0x46b/Polyhymnia/Code/Polyhymnia/src/Settings.cpp

#include "Settings.hpp"
#include <ArduinoJson.h>
#include <SD.h>

Settings::Settings(const char *filename) : System() {}

bool Settings::LoadSettings() {
  if (!SD.begin(BUILTIN_SDCARD)) {
    Serial.println("initialization failed!");
    _loadedSuccessfully = false;
    return false;
  }

  File input = SD.open(_filename, FILE_READ);
  JsonDocument doc;

  DeserializationError error = deserializeJson(doc, input);
  input.close();

  if (error) {
    Serial.print("deserializeJson() failed: ");
    Serial.println(error.c_str());
    return false;
  }

  JsonObject settings = doc["settings"];
  System.ShowBootscreen = settings["ShowBootscreen"];         // "true"
  System.BootscreenFilepath = settings["BootscreenFilepath"]; // nullptr
  System.MidiChannel = settings["MidiChannel"];               // 1

  int patchCounter = 0;
  for (JsonObject patche : doc["patches"].as<JsonArray>()) {
    PatchSetting *currentPatch = &Patches[patchCounter];
    currentPatch->Name = patche["Name"]; // "Patch 1", "Patch 2"

    currentPatch->DCO1.Waveform = patche["VCO1"]["Type"]; // 1, 1
    currentPatch->DCO1.Detune = patche["VCO1"]["Detune"]; // 0, 0

    currentPatch->DCO2.Waveform = patche["VCO2"]["Type"]; // 1, 1
    currentPatch->DCO2.Detune = patche["VCO2"]["Detune"]; // 0, 0

    currentPatch->DCO3.Waveform = patche["VCO3"]["Type"]; // 1, 1
    currentPatch->DCO3.Detune = patche["VCO3"]["Detune"]; // 0, 0

    currentPatch->Noise.Gain = patche["Noise"]["Gain"]; // 0, 0

    JsonObject patche_Envelope = patche["Envelope"];
    currentPatch->Envelope.Attack = patche_Envelope["Attack"];   // 0, 0
    currentPatch->Envelope.Decay = patche_Envelope["Decay"];     // 35, 35
    currentPatch->Envelope.Sustain = patche_Envelope["Sustain"]; // 1, 1
    currentPatch->Envelope.Release = patche_Envelope["Release"]; // 300, 300

    JsonObject patche_Filter = patche["Filter"];
    currentPatch->Filter.Type = patche_Filter["FilterType"];     // 0, 0
    currentPatch->Filter.Cutoff = patche_Filter["Cutoff"];       // 1, 1
    currentPatch->Filter.Resonance = patche_Filter["Resonance"]; // 0, 0

    currentPatch->LFO.Rate = patche["LFO"]["Rate"];     // 10, 10
    currentPatch->LFO.Amount = patche["LFO"]["Amount"]; // 50, 50

    JsonObject patche_Mixer = patche["Mixer"];
    currentPatch->Mixer.DCO1Gain = patche_Mixer["VCO1Gain"];   // 0.3, 0.3
    currentPatch->Mixer.DCO2Gain = patche_Mixer["VCO2Gain"];   // 0.3, 0.3
    currentPatch->Mixer.DCO3Gain = patche_Mixer["VCO3Gain"];   // 0.3, 0.3
    currentPatch->Mixer.NoiseGain = patche_Mixer["NoiseGain"]; // 0, 0

    patchCounter++;
  }

  _loadedSuccessfully = true;
  return true;
}

bool Settings::Save() {
  JsonDocument doc;

  JsonObject settings = doc["settings"].to<JsonObject>();
  settings["ShowBootscreen"] = System.ShowBootscreen;
  settings["BootscreenFilepath"] = System.BootscreenFilepath;
  settings["MidiChannel"] = System.MidiChannel;

  JsonArray patches = doc["patches"].to<JsonArray>();

  for (int i = 0; i <= NUMBER_OF_PATCHES; i++) {
    JsonObject patches_0 = patches.add<JsonObject>();
    patches_0["Name"] = Patches[i].Name;

    JsonObject patches_0_VCO1 = patches_0["DCO1"].to<JsonObject>();
    patches_0_VCO1["Type"] = Patches[i].DCO1.Waveform;
    patches_0_VCO1["Detune"] = Patches[i].DCO1.Detune;

    JsonObject patches_0_VCO2 = patches_0["DCO2"].to<JsonObject>();
    patches_0_VCO2["Type"] = Patches[i].DCO2.Waveform;
    patches_0_VCO2["Detune"] = Patches[i].DCO2.Detune;

    JsonObject patches_0_VCO3 = patches_0["DCO3"].to<JsonObject>();
    patches_0_VCO3["Type"] = Patches[i].DCO3.Waveform;
    patches_0_VCO3["Detune"] = Patches[i].DCO3.Detune;
    patches_0["Noise"]["Gain"] = Patches[i].Noise.Gain;

    JsonObject patches_0_Envelope = patches_0["Envelope"].to<JsonObject>();
    patches_0_Envelope["Attack"] = Patches[i].Envelope.Attack;
    patches_0_Envelope["Decay"] = Patches[i].Envelope.Decay;
    patches_0_Envelope["Sustain"] = Patches[i].Envelope.Sustain;
    patches_0_Envelope["Release"] = Patches[i].Envelope.Release;

    JsonObject patches_0_Filter = patches_0["Filter"].to<JsonObject>();
    patches_0_Filter["FilterType"] = Patches[i].Filter.Type;
    patches_0_Filter["Cutoff"] = Patches[i].Filter.Cutoff;
    patches_0_Filter["Resonance"] = Patches[i].Filter.Resonance;

    JsonObject patches_0_LFO = patches_0["LFO"].to<JsonObject>();
    patches_0_LFO["Rate"] = Patches[i].LFO.Rate;
    patches_0_LFO["Amount"] = Patches[i].LFO.Amount;

    JsonObject patches_0_Mixer = patches_0["Mixer"].to<JsonObject>();
    patches_0_Mixer["DCO1Gain"] = Patches[i].Mixer.DCO1Gain;
    patches_0_Mixer["DCO2Gain"] = Patches[i].Mixer.DCO2Gain;
    patches_0_Mixer["DCO3Gain"] = Patches[i].Mixer.DCO3Gain;
    patches_0_Mixer["NoiseGain"] = Patches[i].Mixer.NoiseGain;
  }

  String output;

  doc.shrinkToFit(); // optional

  serializeJson(doc, output);
  File outputFile = SD.open(_filename, FILE_WRITE);
  if (outputFile) {
    outputFile.print(output.c_str());

    outputFile.close();
    return true;
  }
  return false;
}

bool Settings::is_loaded() { return _loadedSuccessfully; }
