0x46b/Polyhymnia/Code/Polyhymnia/include/MIDI.hpp

#ifndef MIDI_HPP
#define MIDI_HPP
#include "Constants.hpp"
#include <cstdint>

namespace MIDI {
/* Lookup-table to match a MIDI-value to the corresponding frequency of the note
 */
const float midiToFrequency[128] = {
    8.176,    8.662,    9.177,    9.723,    10.301,   10.913,   11.562,
    12.25,    12.978,   13.75,    14.568,   15.434,   16.352,   17.324,
    18.354,   19.445,   20.602,   21.827,   23.125,   24.5,     25.957,
    27.5,     29.135,   30.868,   32.703,   34.648,   36.708,   38.891,
    41.203,   43.654,   46.249,   48.999,   51.913,   55,       58.27,
    61.735,   65.406,   69.296,   73.416,   77.782,   82.407,   87.307,
    92.499,   97.999,   103.826,  110,      116.541,  123.471,  130.813,
    138.591,  146.832,  155.563,  164.814,  174.614,  184.997,  195.998,
    207.652,  220,      233.082,  246.942,  261.626,  277.183,  293.665,
    311.127,  329.628,  349.228,  369.994,  391.995,  415.305,  440,
    466.164,  493.883,  523.251,  554.365,  587.33,   622.254,  659.255,
    698.456,  739.989,  783.991,  830.609,  880,      932.328,  987.767,
    1046.502, 1108.731, 1174.659, 1244.508, 1318.51,  1396.913, 1479.978,
    1567.982, 1661.219, 1760,     1864.655, 1975.533, 2093.005, 2217.461,
    2349.318, 2489.016, 2637.02,  2793.826, 2959.955, 3135.963, 3322.438,
    3520,     3729.31,  3951.066, 4186.009, 4434.922, 4698.636, 4978.032,
    5274.041, 5587.652, 5919.911, 6271.927, 6644.875, 7040,     7458.62,
    7902.133, 8372.018, 8869.844, 9397.273, 9956.063, 10548.08, 11175.3,
    11839.82, 12543.85};

/*! Converts a MIDI-value to the correct frequency of the note
 * \returns The corresponding frequency
 * \param[in] midiValue Note-value given by the MIDI-system (0-127)
 */
float midivalue_to_frequency(uint8_t midiValue);

/*! Scales the given value linear to a range 0-maxValue
 *
 * \returns mapped value
 * \param[in] value The value that should get scaled (0-127)
 * \param[in] maxValue Maximum value (e.g. value = 127 => maxValue)
 * \param[in] offset Shifts the entire output range up or down so that the
 * minimum input yields the offset value rather than zero
 */
float scale_cc_linear(uint8_t value, float maxValue, float offset);

} // namespace MIDI
#endif
